abhishekchak52/ssc-evm/SD_test/SD_test.ino

/* @file CustomKeypad.pde
|| @version 1.0
|| @author Alexander Brevig
|| @contact alexanderbrevig@gmail.com
||
|| @description
|| | Demonstrates changing the keypad size and key values.
|| #
*/
#include <Keypad.h>
#include <LiquidCrystal.h>
#include <SPI.h>
#include <SD.h>

const byte ROWS = 4; //four rows
const byte COLS = 4; //four columns
//define the cymbols on the buttons of the keypads
char hexaKeys[ROWS][COLS] = {
  {'1','2','3','A'},
  {'4','5','6','B'},
  {'7','8','9','C'},
  {'*','0','#','D'}
};
byte rowPins[ROWS] = {14, 15, 16, 17}; //connect to the row pinouts of the keypad
byte colPins[COLS] = {18, 19, 0, 1}; //connect to the column pinouts of the keypad

//initialize an instance of class NewKeypad
Keypad customKeypad = Keypad( makeKeymap(hexaKeys), rowPins, colPins, ROWS, COLS); 

LiquidCrystal lcd(2,3,4,5,6,7);

File myfile;

void setup(){
  lcd.begin(4,2);
  if(SD.begin(10))
    lcd.print("SD card okay!");
  delay(1000);
}
  
void loop(){
  char customKey = customKeypad.getKey();
  if (customKey){
//    lcd. clear();
    lcd.write(customKey);
  }
}
